SiliconLabs/hardware_design_examples/EFR32xG22_QFN40_2p4GHz_6dBm_2layers_BLE_ESL_Node/PDF/EFR32xG22_ESL-Node_Ref-Des_SCH.pdf

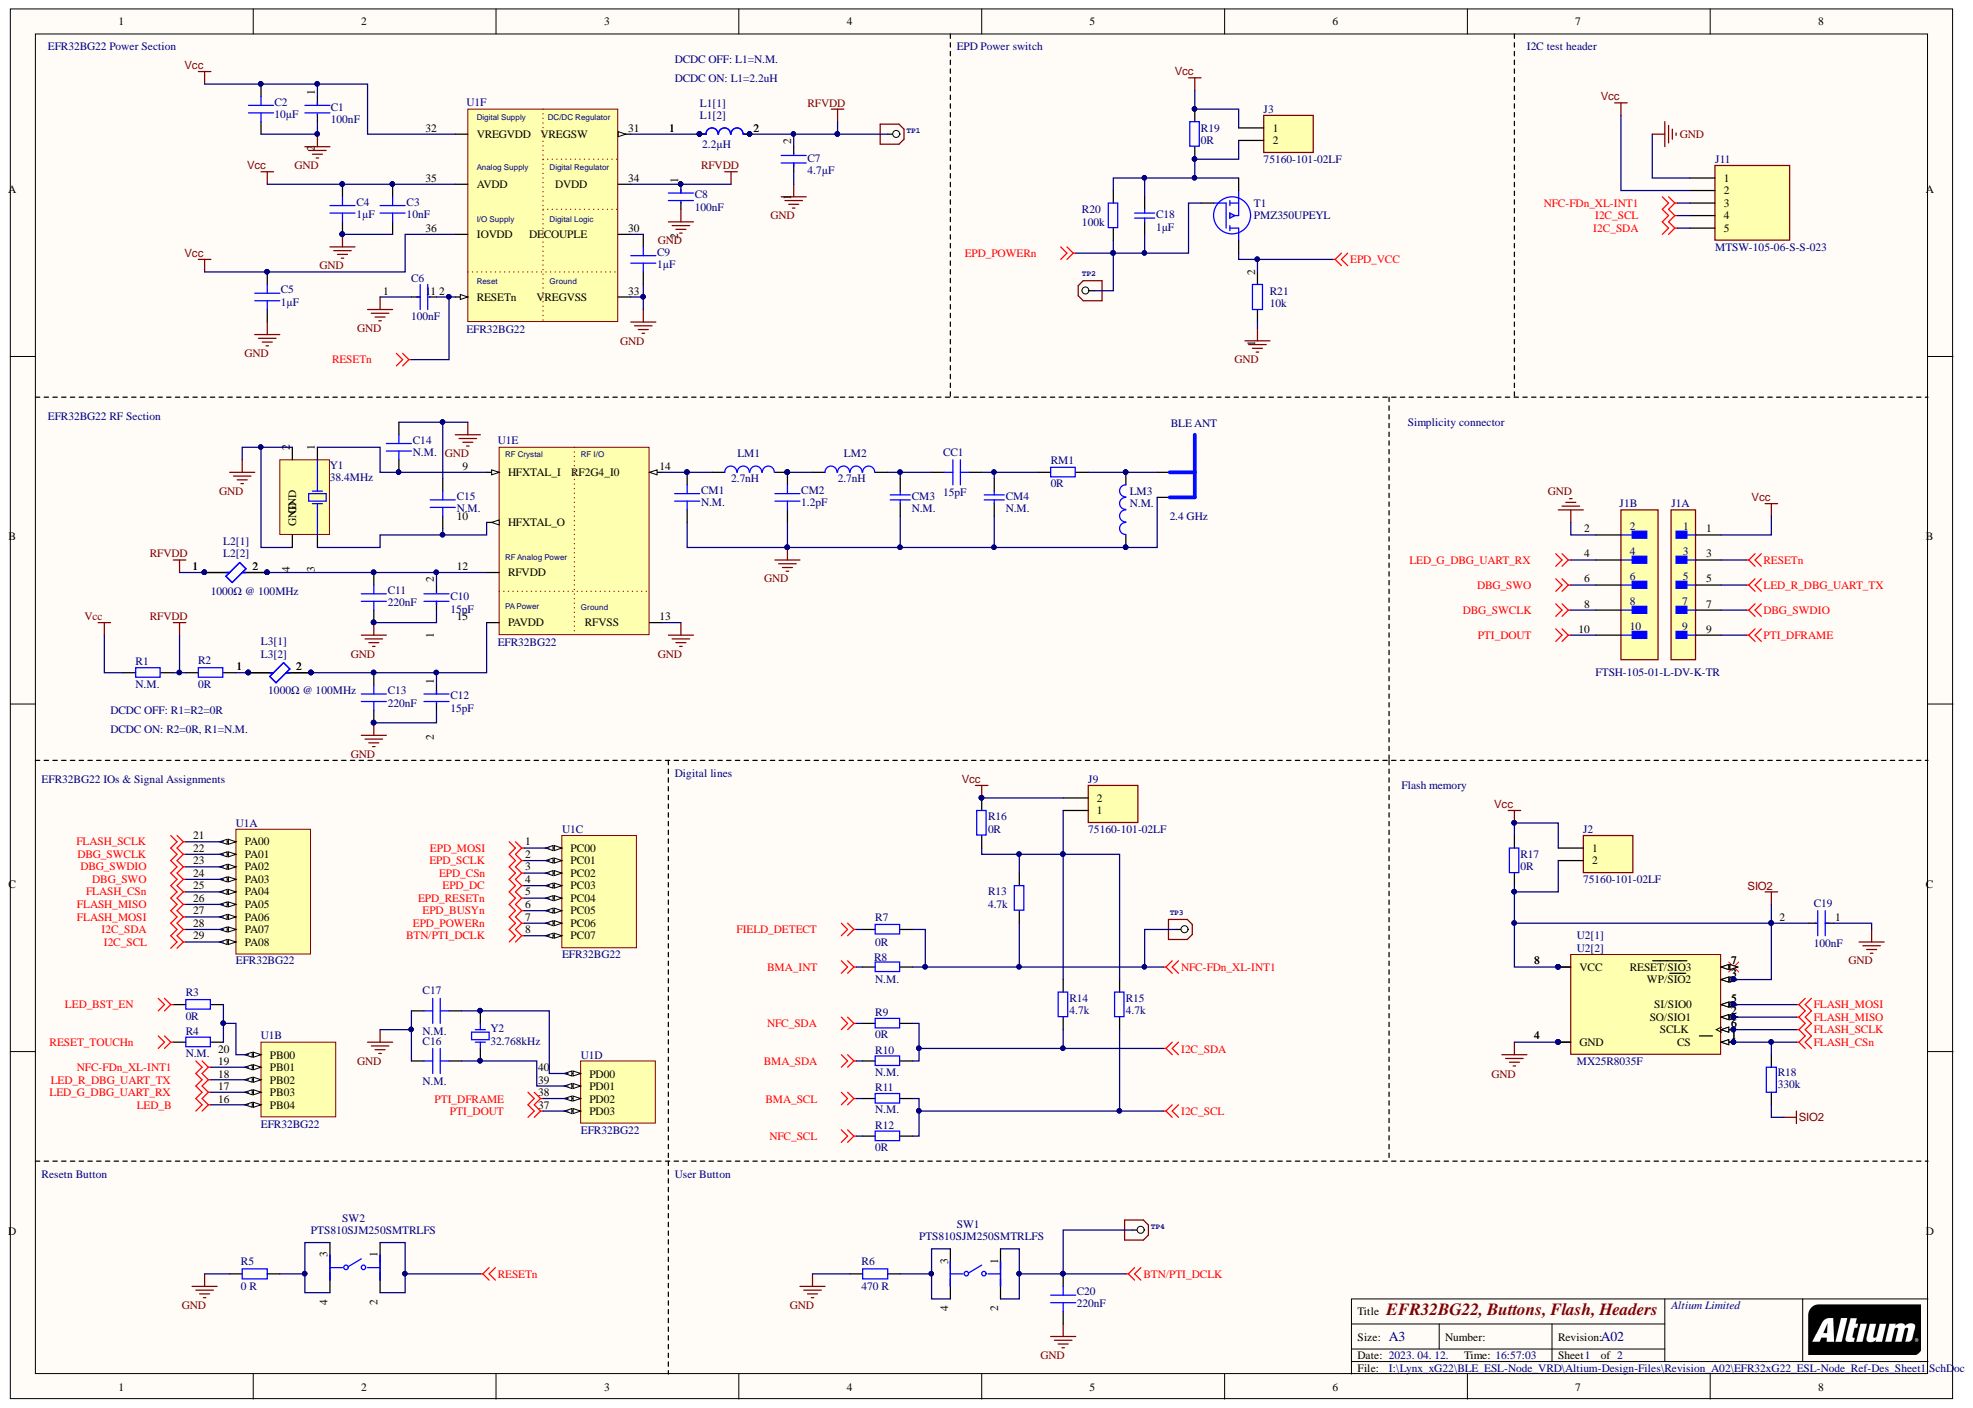
[picture p1: page 1]

GND

Reset | Ground

EFR32BG22, Buttons, Flash, Headers Title | Altium Limited

Size: A3 | Number: | Revision: A02
Date: 2023. 04. 12. Time: 16:57:03 | | Sheet 1 of 2

I:\Lynx_xG22\BLE_ESL-Node_VRD\Altium-Design-Files\Revision_A02\EFR32xG22_ESL-Node_Ref-Des_Sheet1.SchDoc

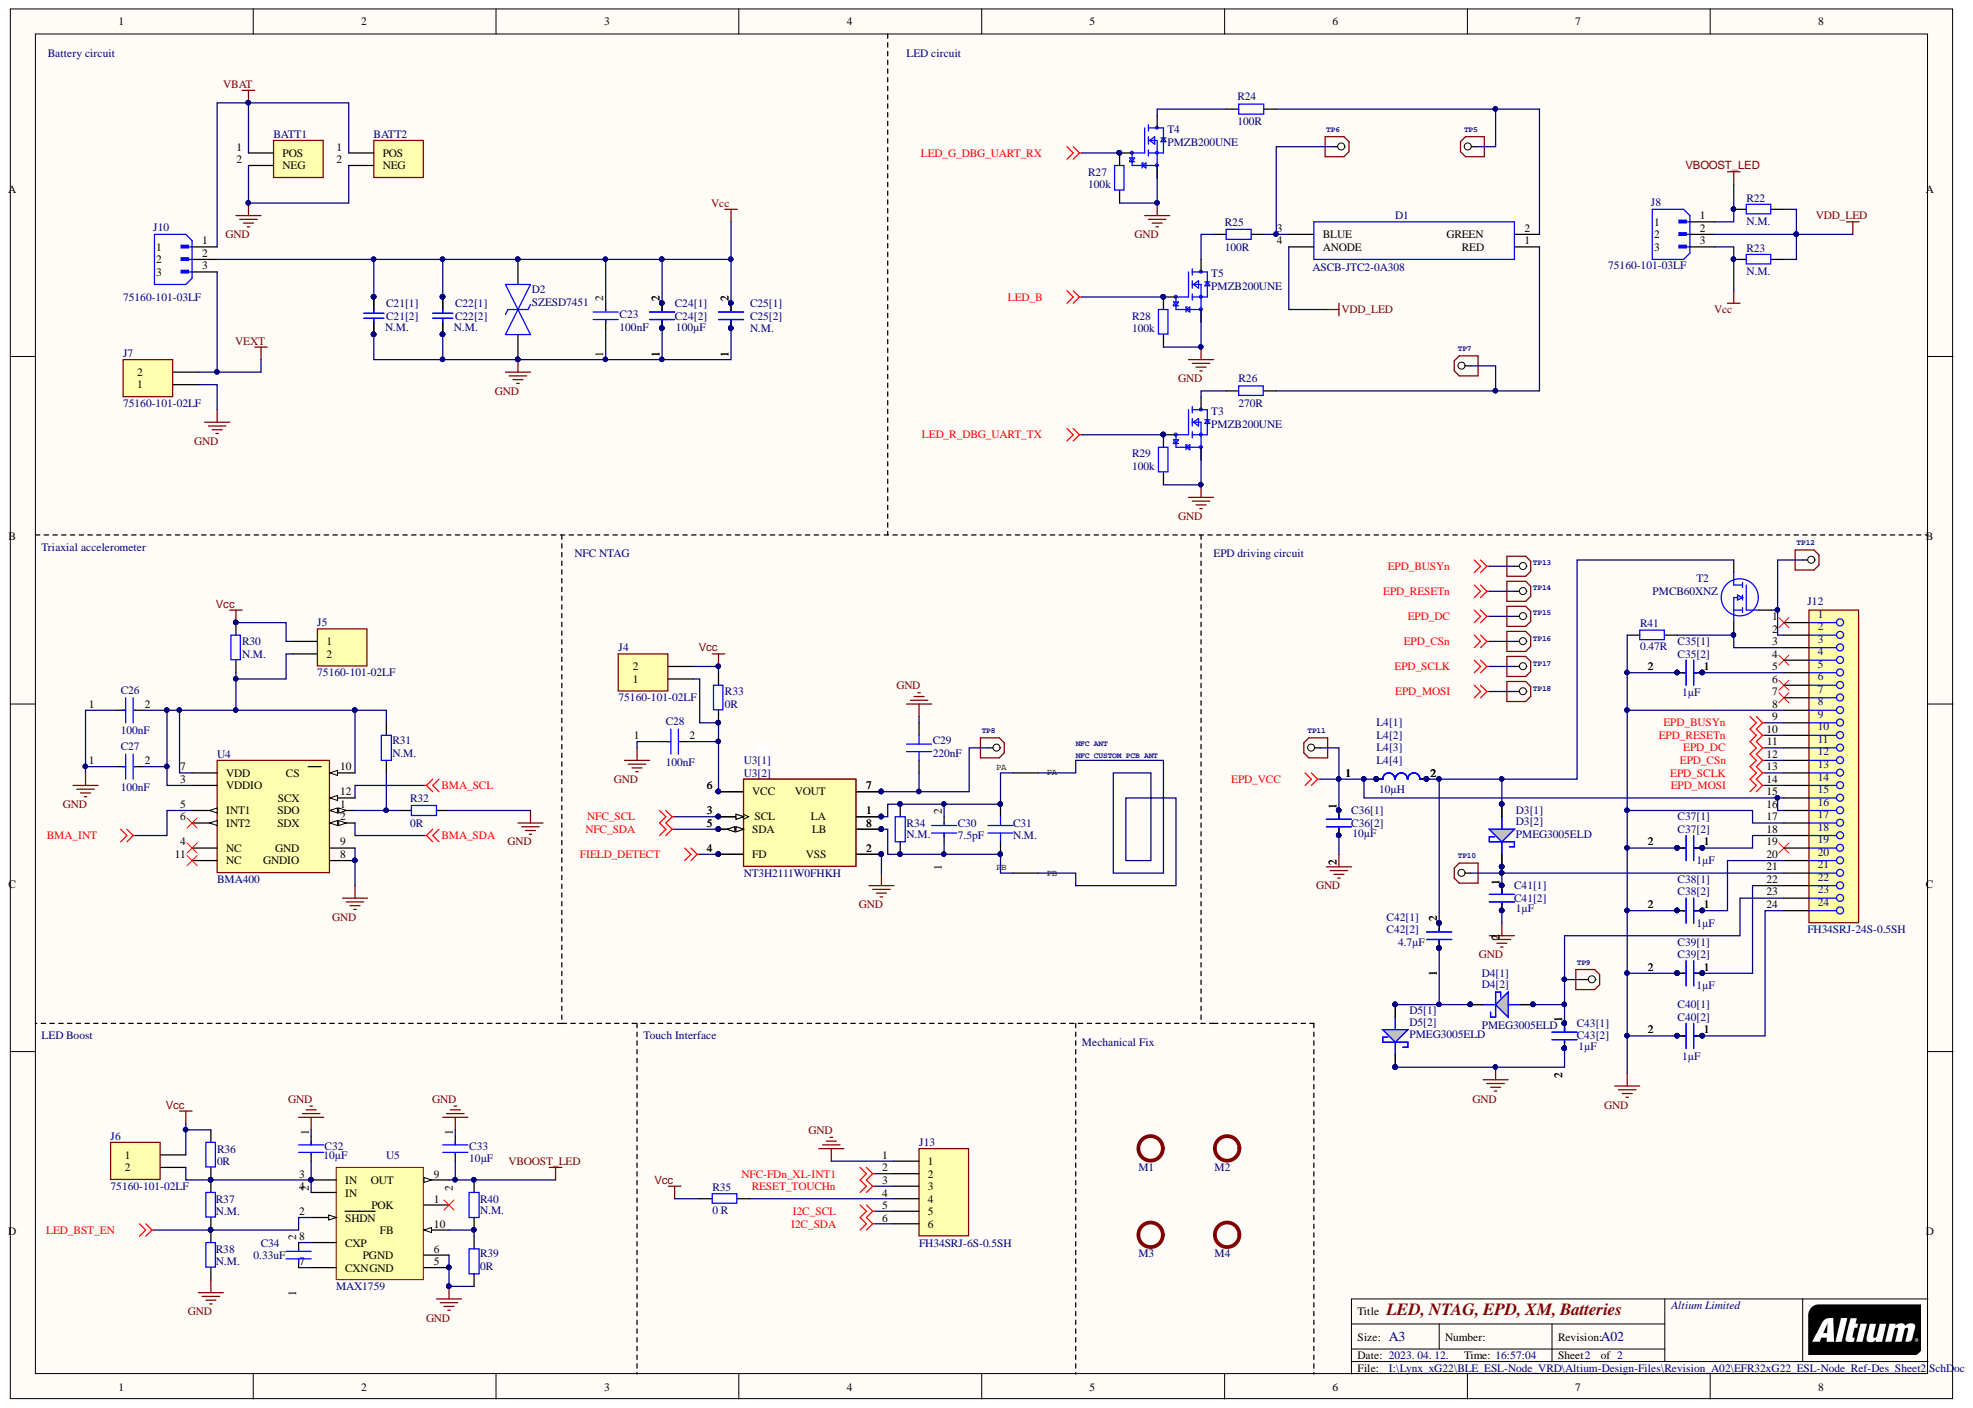
[picture p2: page 2]

BATT1

NFC ANT
NFC CUSTOM PCB ANT

LED, NTAG, EPD, XM, Batteries Title | Altium Limited

Size: A3 | Number: | Revision: A02
Date: 2023. 04. 12. Time: 16:57:04 | | Sheet 2 of 2

I:\Lynx_xG22\BLE_ESL-Node_VRD\Altium-Design-Files\Revision_A02\EFR32xG22_ESL-Node_Ref-Des_Sheet2.SchDoc
