SiliconLabs/hardware_design_examples/EFR32xG22_QFN32_2p4GHz_6dBm_4layers_BLE_Tag/PDF/EFR32BG22_TAG_REF_DES_A01_SCH.pdf

6 | 5 | 4 | 3 | 2 | 1

D

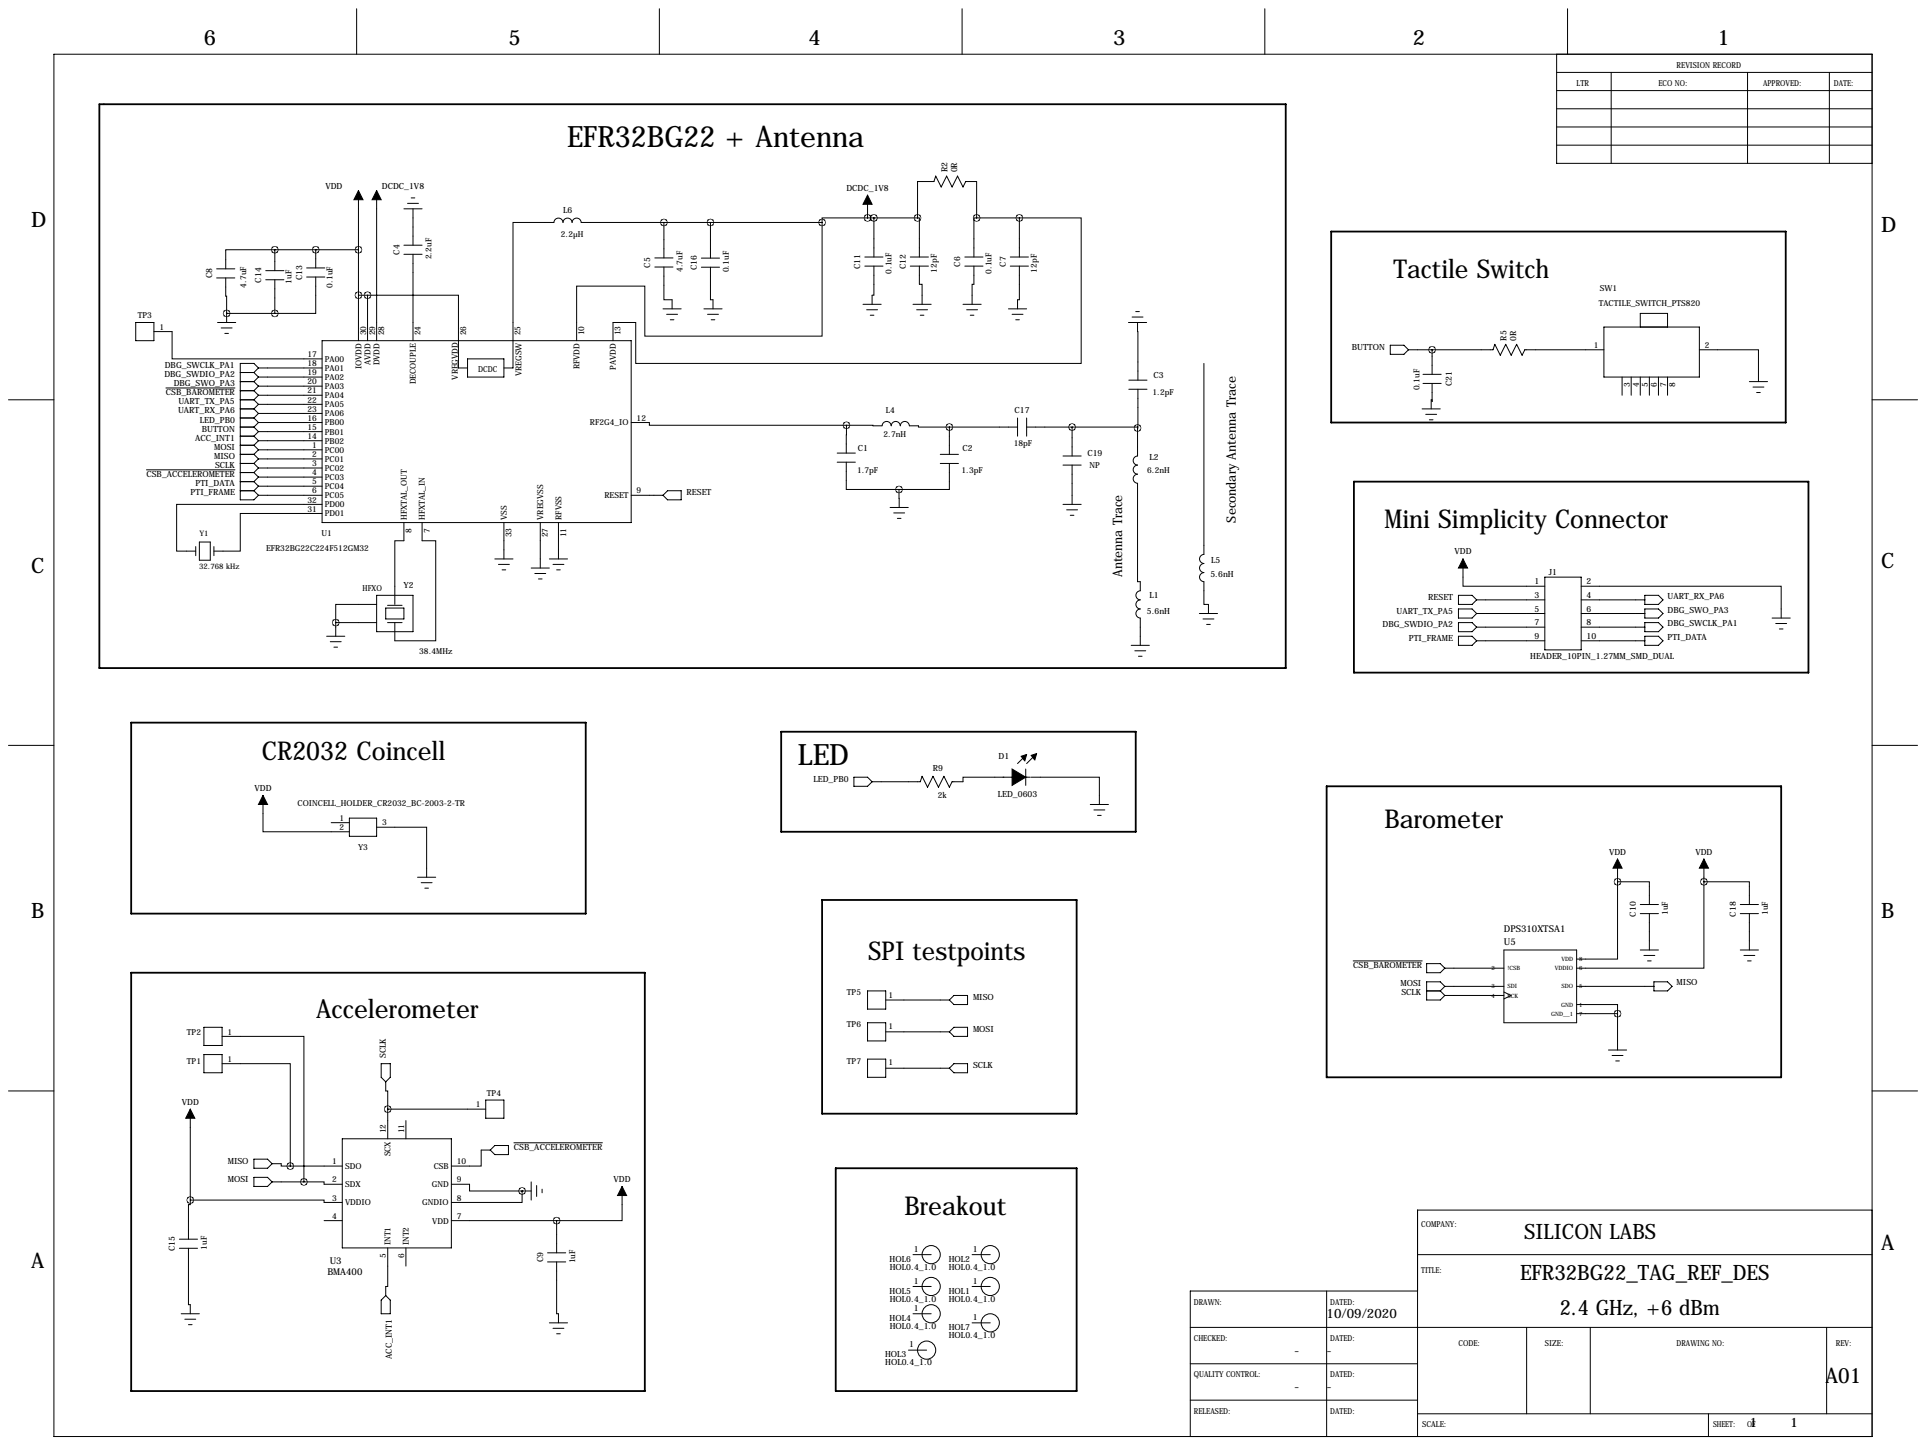
[picture p3: page 1]

REVISION RECORD

LTR | ECO NO: | APPROVED: | DATE:

SPI testpoints

Accelerometer

DRAWN: | DATED: 10/09/2020

CHECKED: - - | DATED: | CODE: | SIZE: | DRAWING NO: | REV: A01

QUALITY CONTROL: - - | DATED:

RELEASED: | DATED:

SCALE: | 1 1 SHEET: OF
