SiliconLabs/hardware_design_examples/EFR32xG22_QFN40_2p4GHz_6dBm_2layers_BLE_ESL_Node/PDF/EFR32xG22_ESL-Node_Ref-Des_PCB.pdf

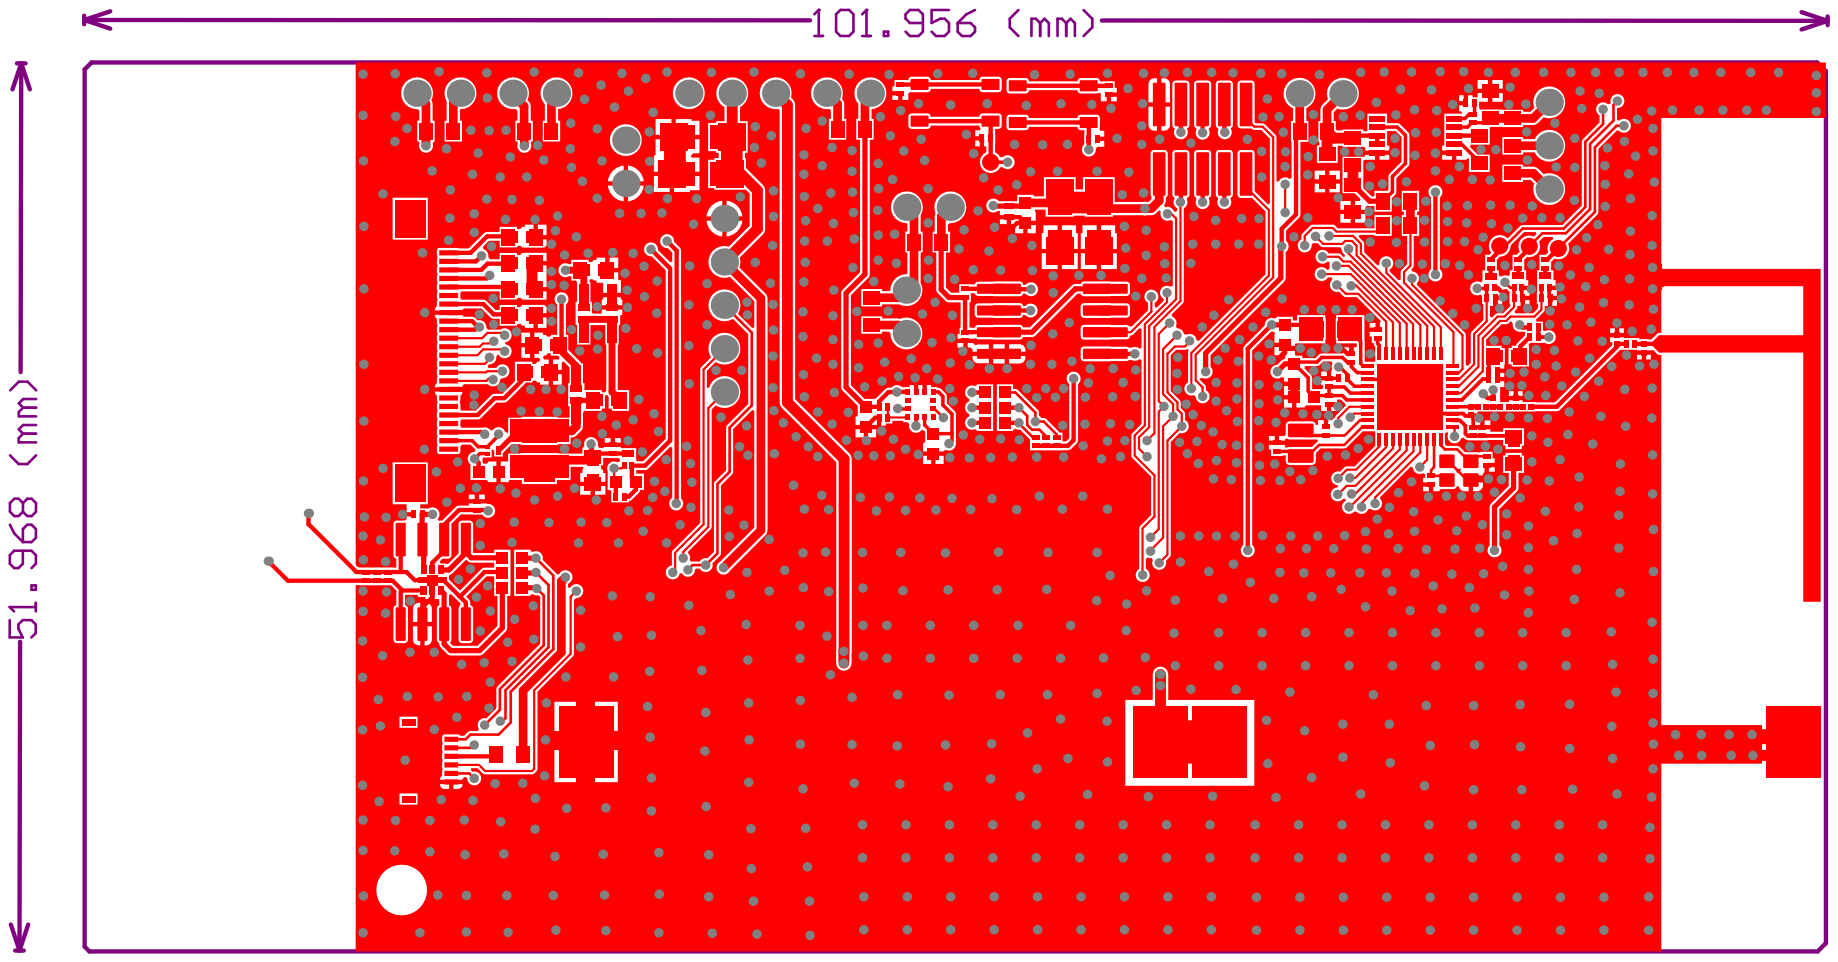
[picture p17: page 1]

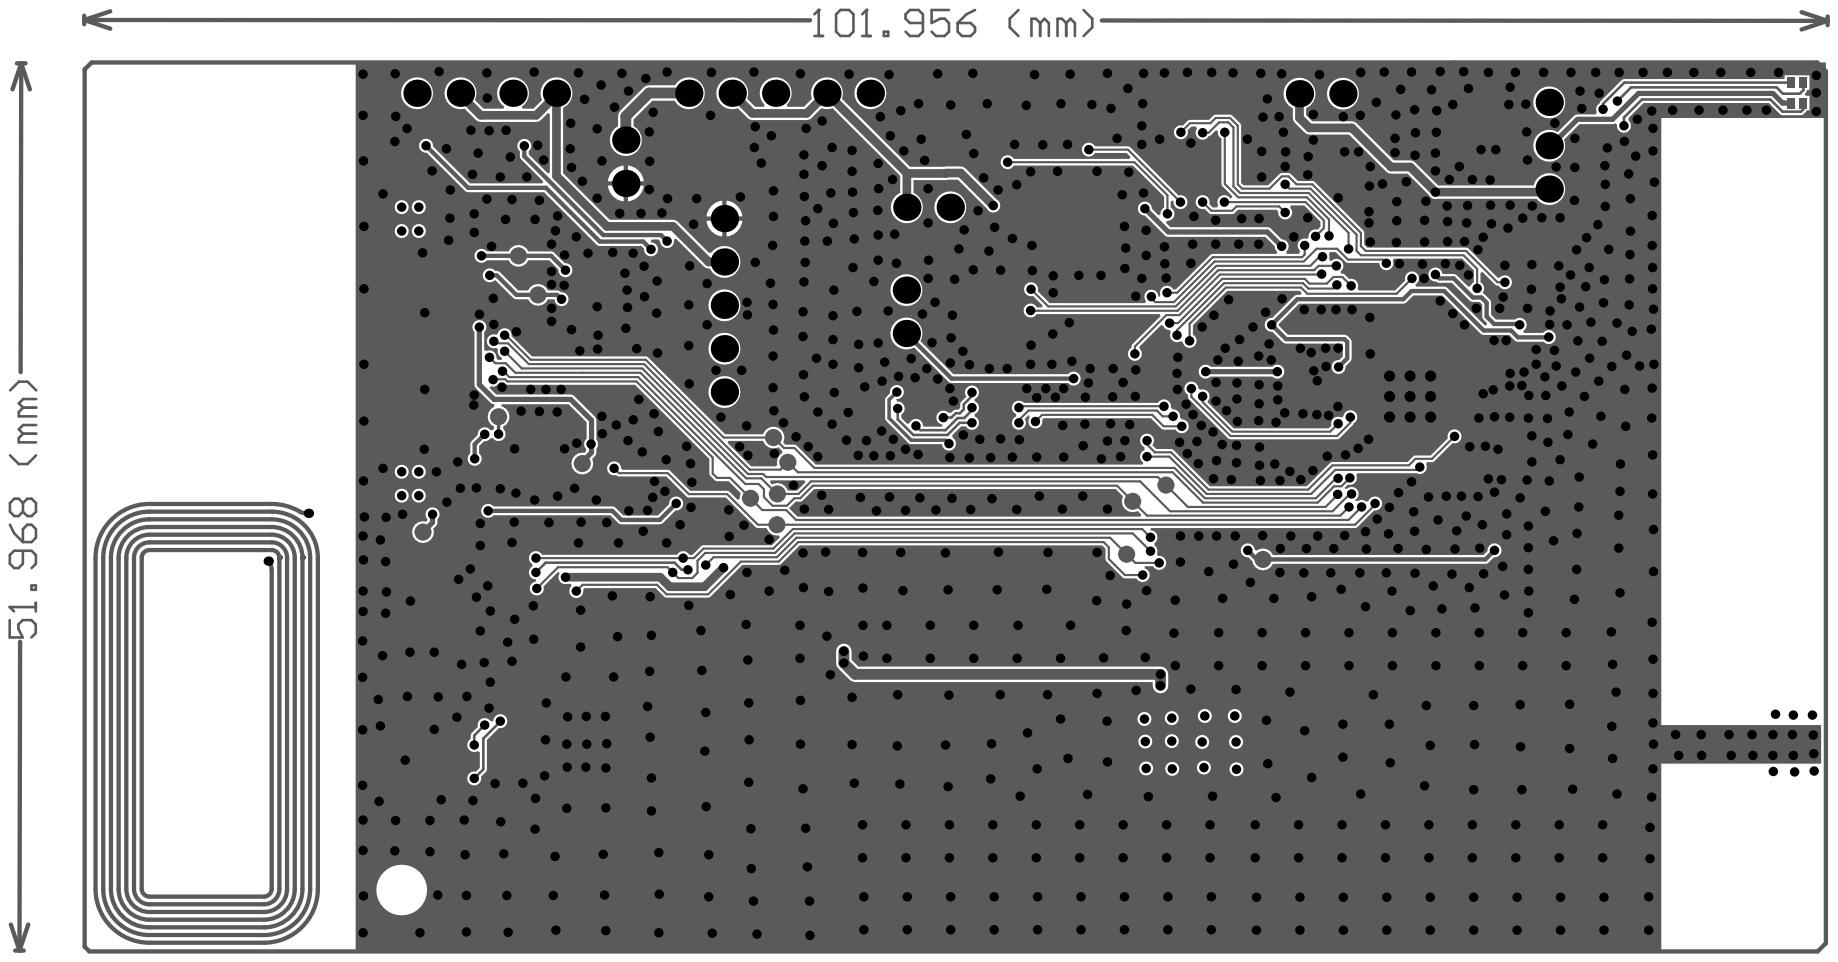
[picture p18: page 2]

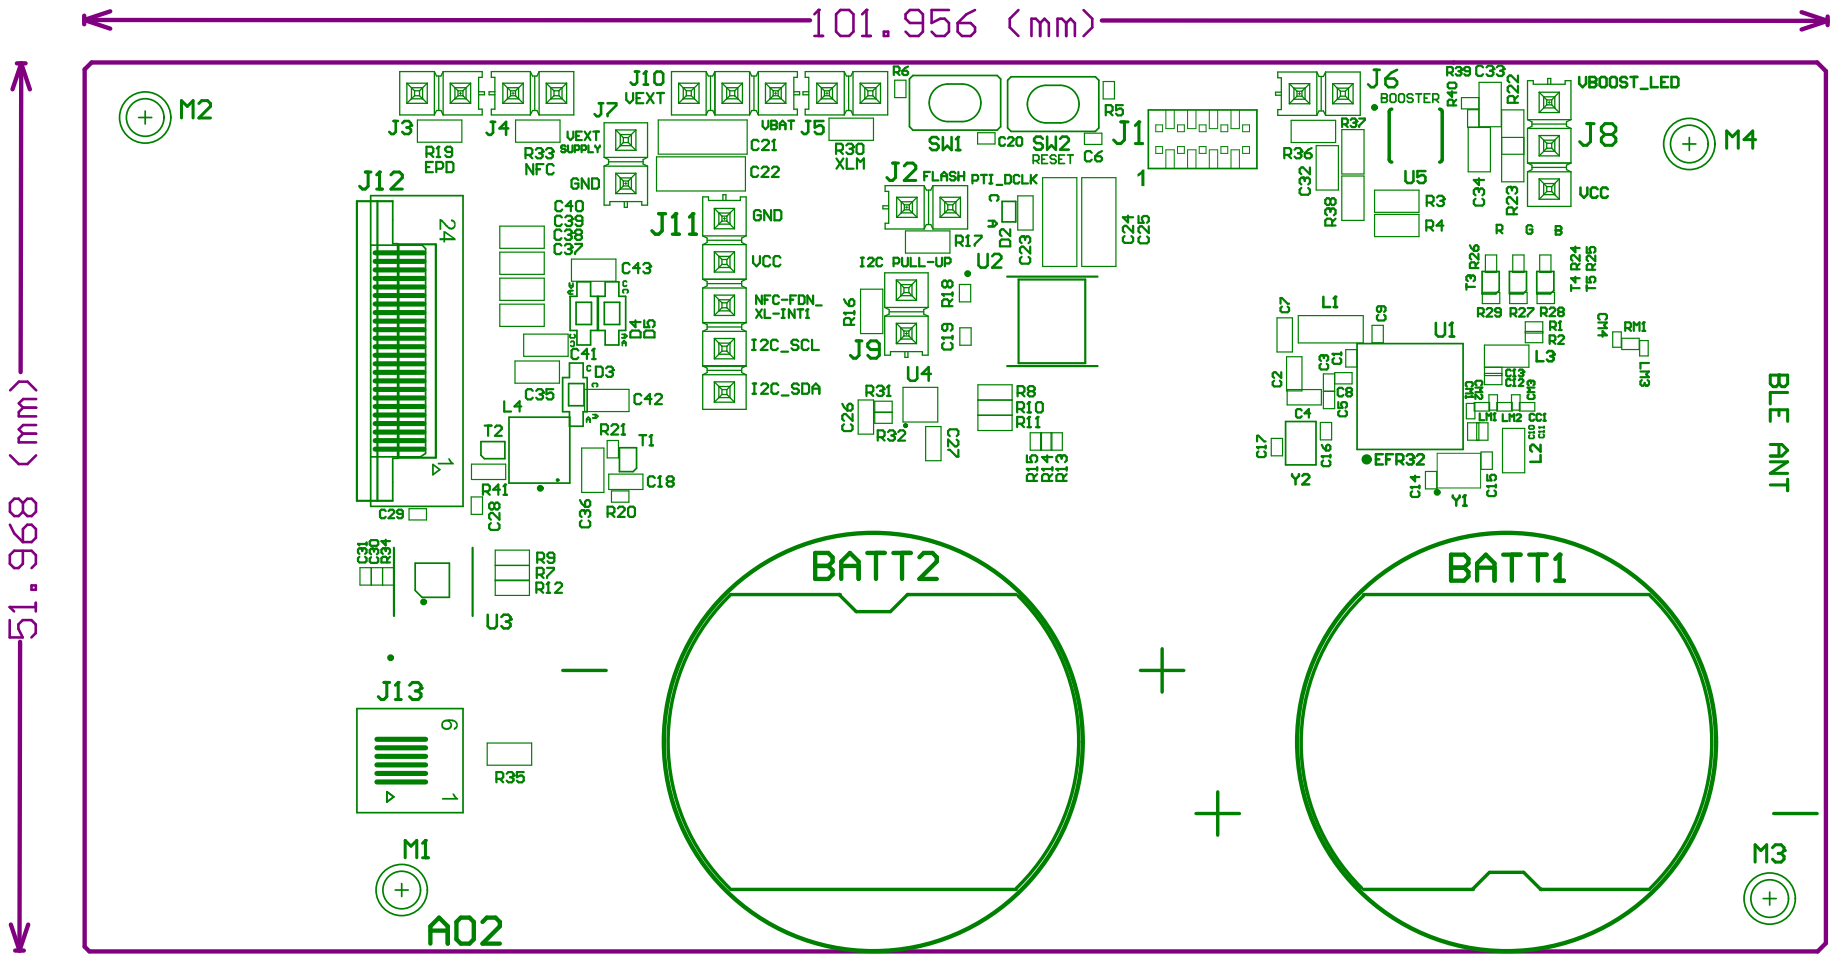
[picture p19: page 3]

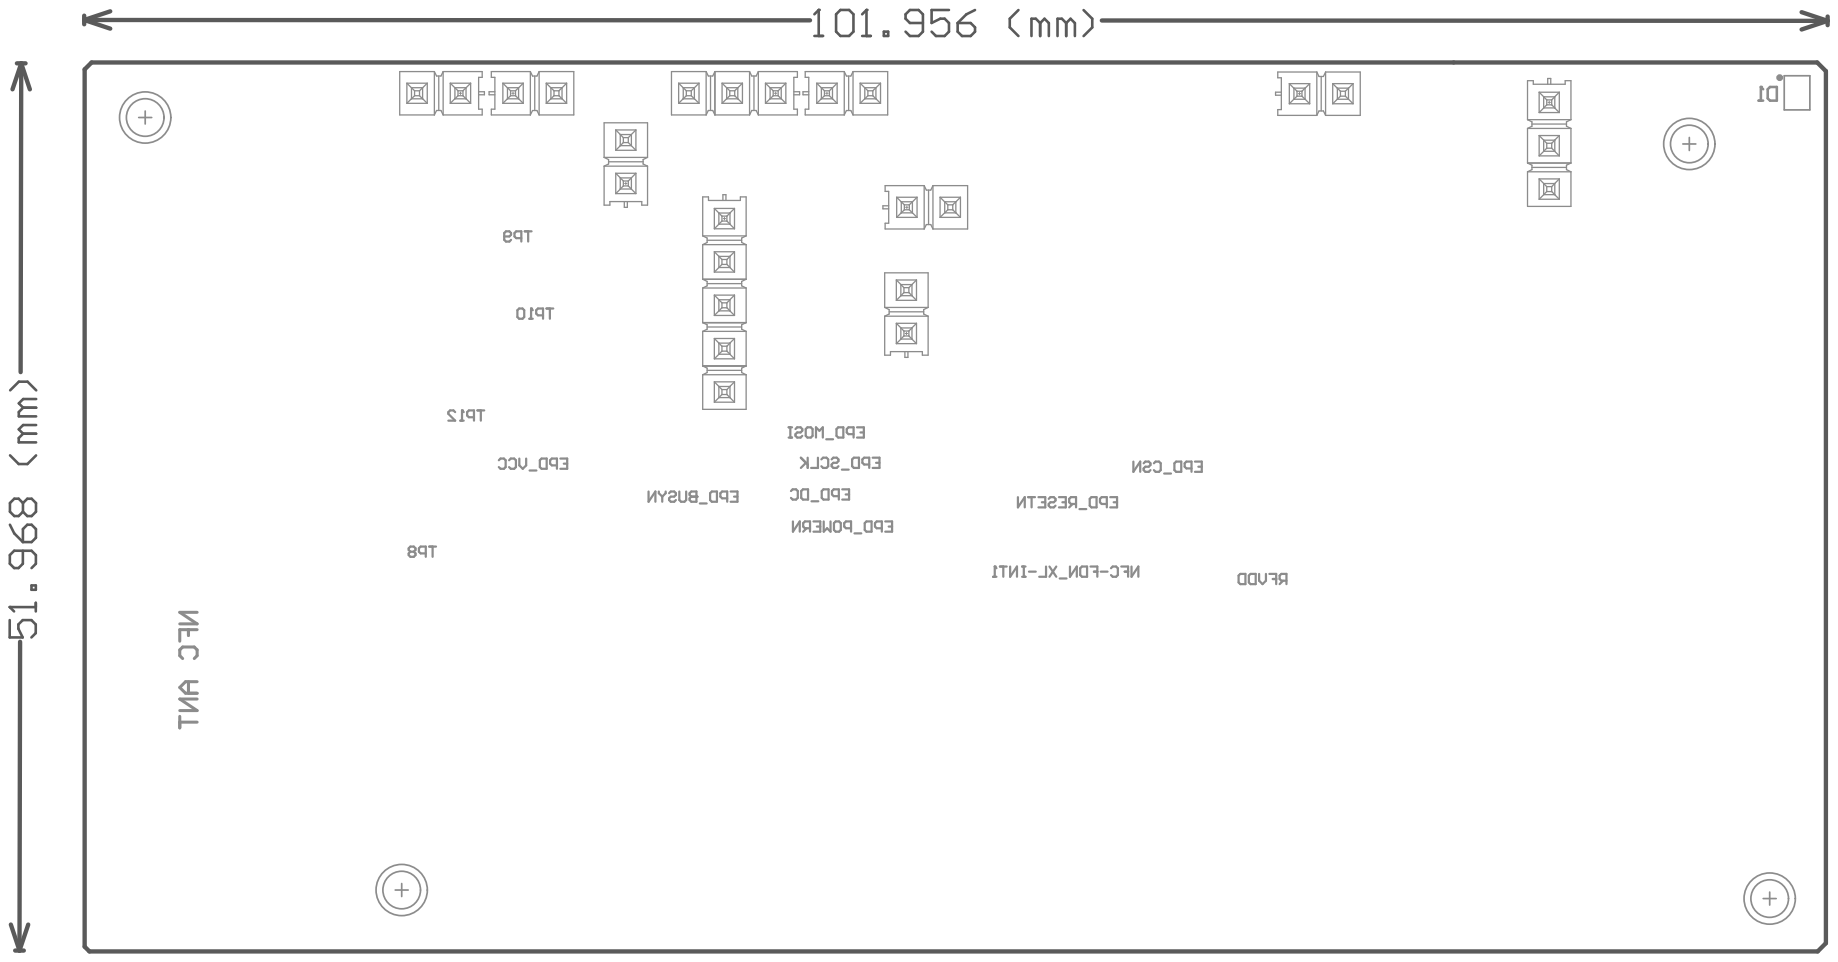
[picture p20: page 4]
